SiddharthK15/TerraFlex/Photos and Videos/Choosing springs for suitable compression.jpg

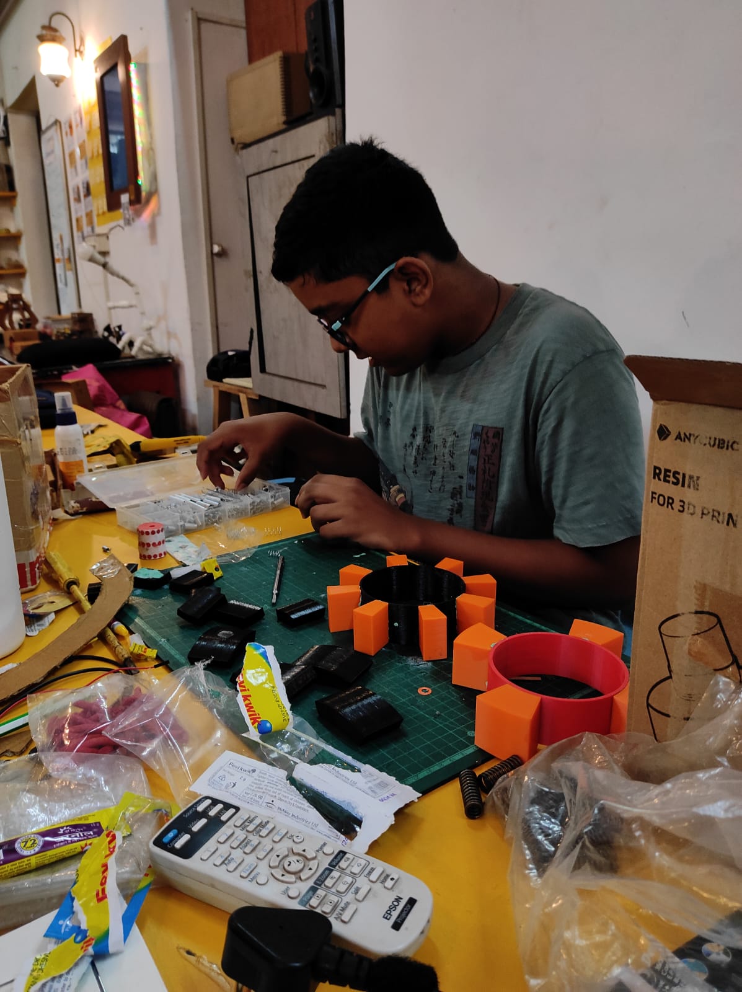
Photos and Videos/Choosing springs for suitable compression.jpg
