SiddharthK15/TerraFlex/Photos and Videos/Different inner tube combinations.jpg

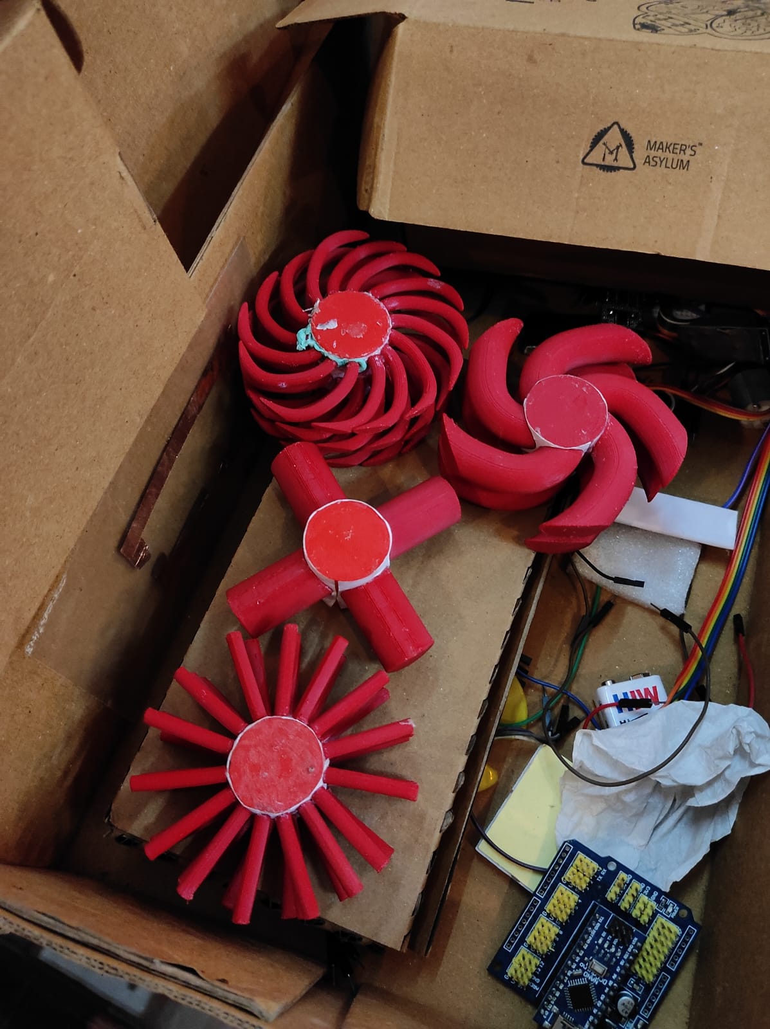
Photos and Videos/Different inner tube combinations.jpg
