SiddharthK15/TerraFlex/Photos and Videos/Side track back angle.jpg

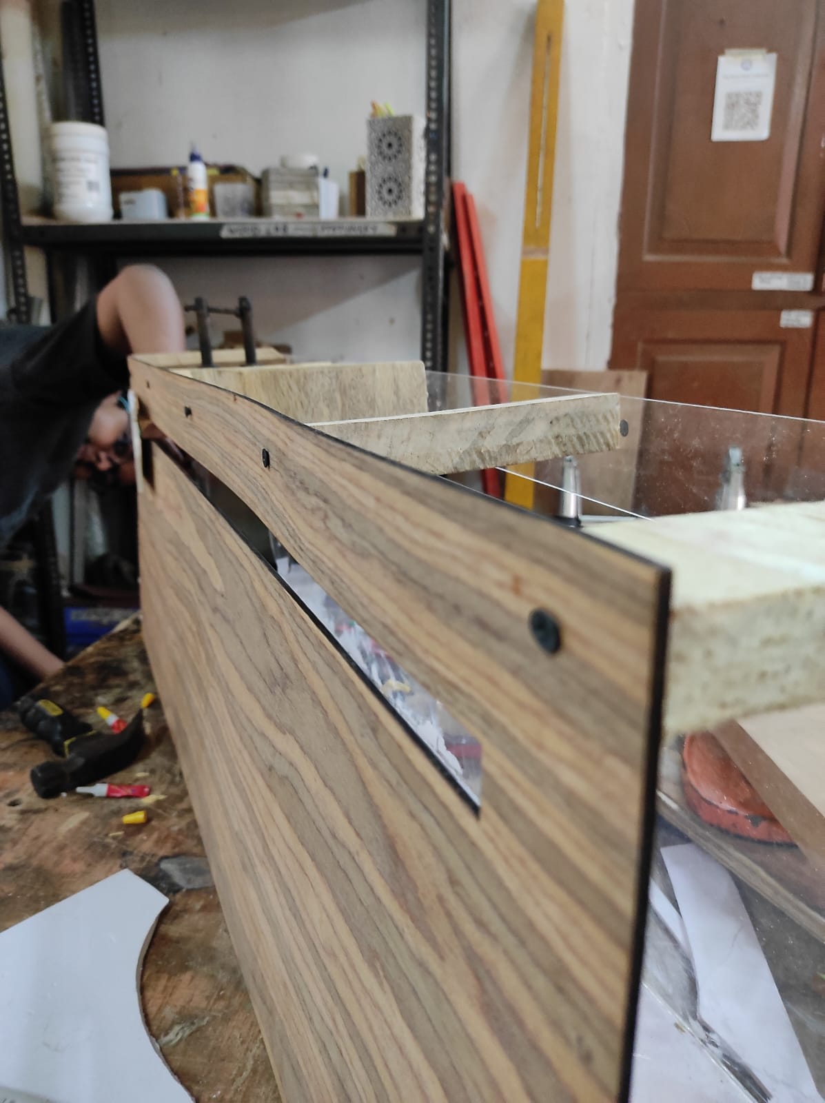
Photos and Videos/Side track back angle.jpg
