SiddharthK15/TerraFlex/Photos and Videos/Side track front angle.jpg

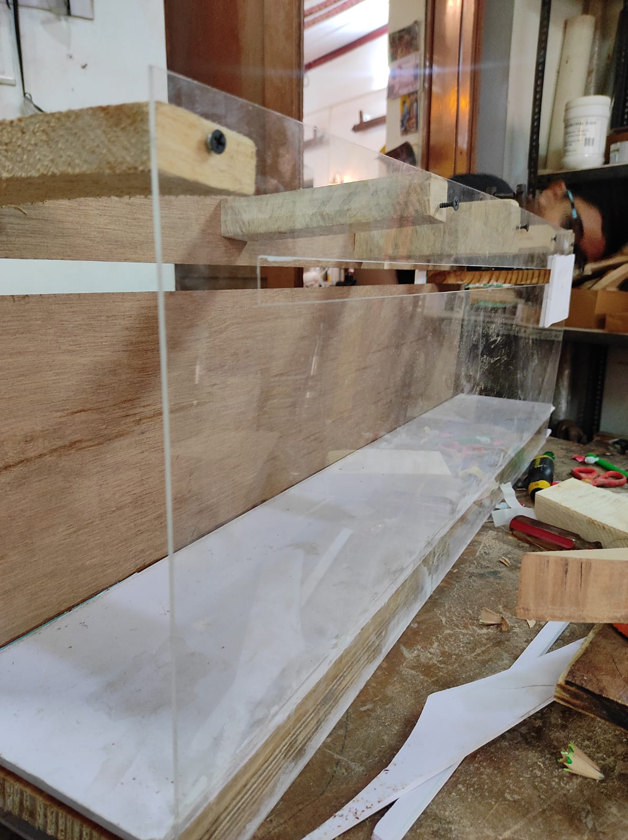
Photos and Videos/Side track front angle.jpg
