SiddharthK15/TerraFlex/Photos and Videos/Applying final touches to the base of test track.jpg

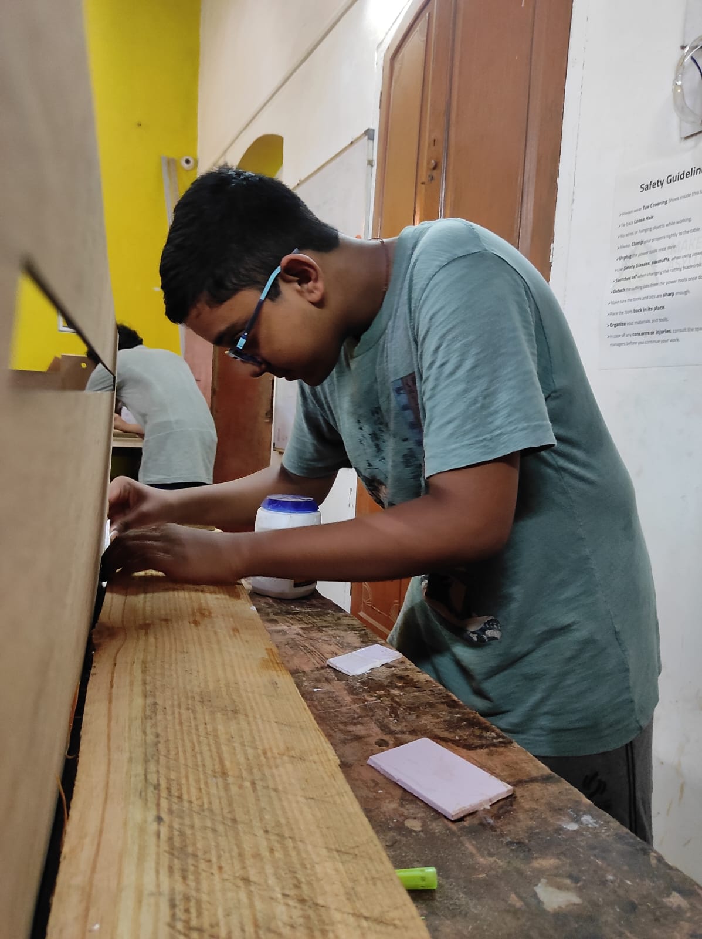
Photos and Videos/Applying final touches to the base of test track.jpg
