SiddharthK15/TerraFlex/Photos and Videos/Initial test track sunboard placement.jpg

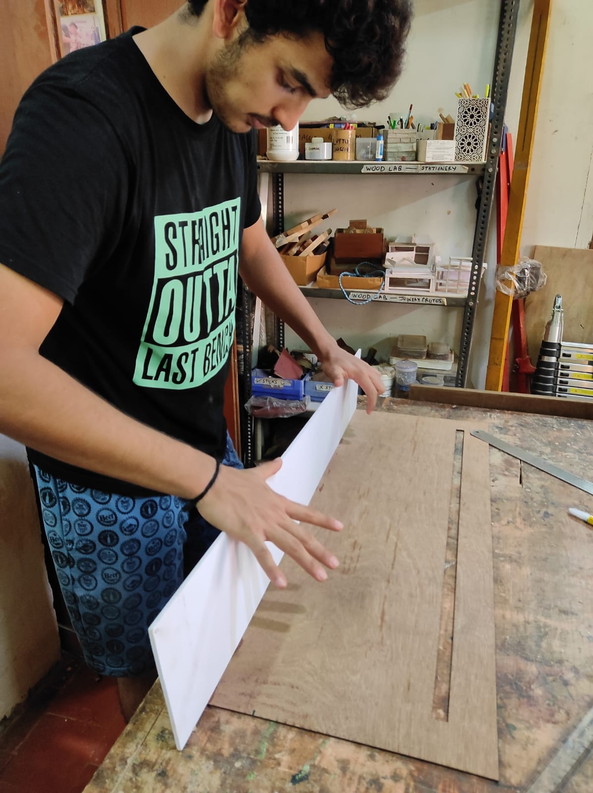
Photos and Videos/Initial test track sunboard placement.jpg
