SiddharthK15/TerraFlex/Photos and Videos/Outer Layer Test Models.jpg

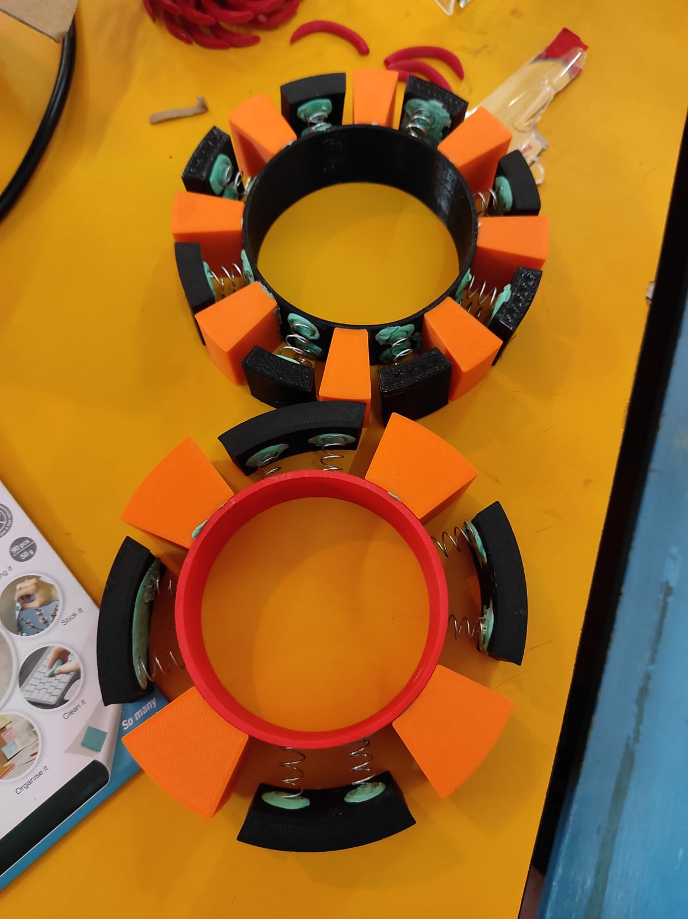
Photos and Videos/Outer Layer Test Models.jpg
