SiddharthK15/TerraFlex/Photos and Videos/Sanding Supports for Test Track.jpg

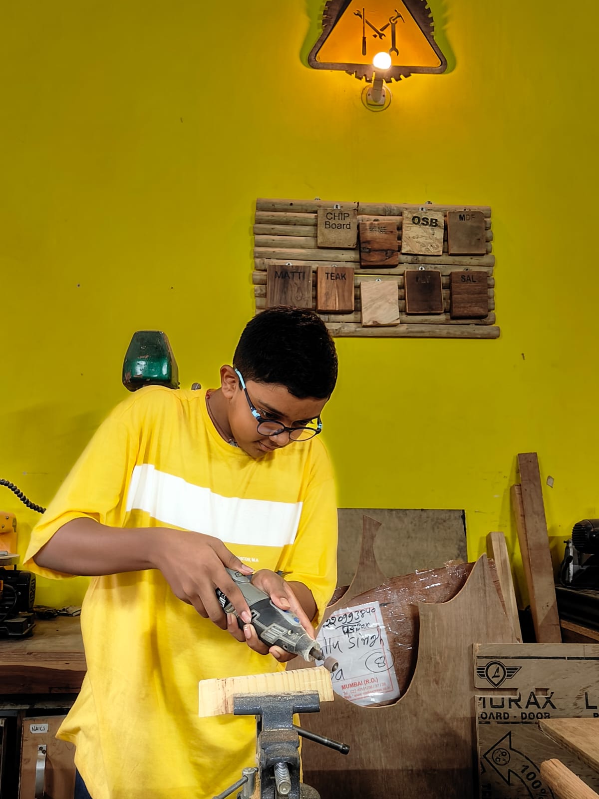
Photos and Videos/Sanding Supports for Test Track.jpg
