SiddharthK15/TerraFlex/Photos and Videos/Taking measurements for slider slit.jpg

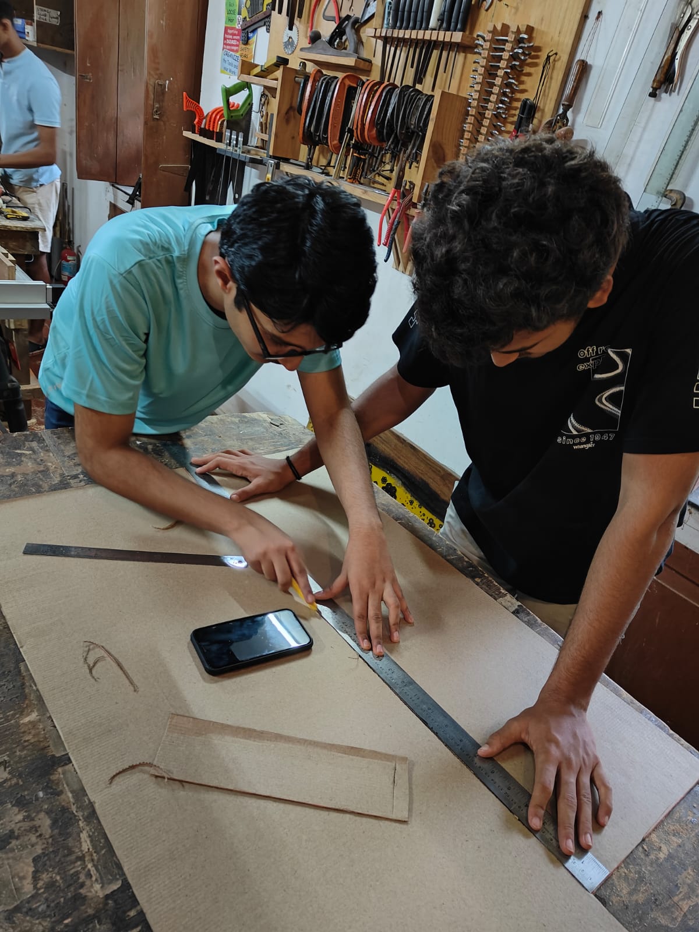
Photos and Videos/Taking measurements for slider slit.jpg
